zaphi/Grilloino2000/Blink_App/blynk.jpg

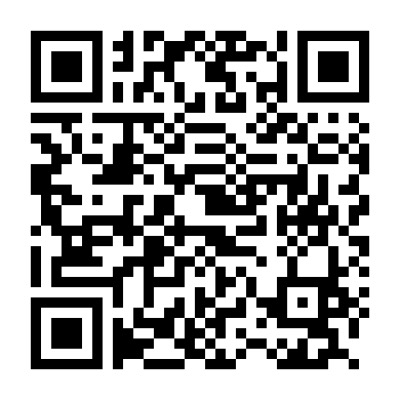
Blink_App/blynk.jpg
