zaphi/Grilloino2000/img/IMG_0674.jpg

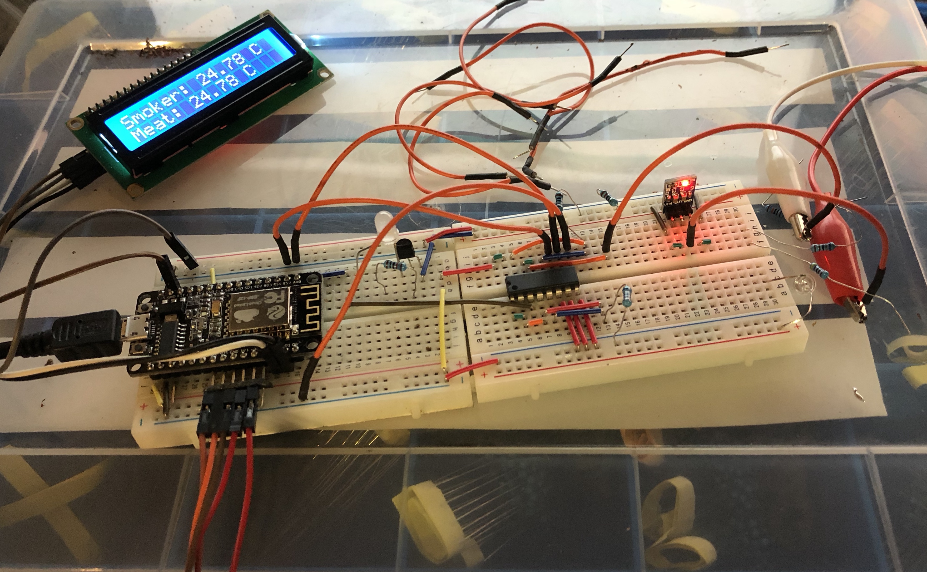
img/IMG_0674.jpg
