zaphi/Grilloino2000/img/IMG_0751.jpg

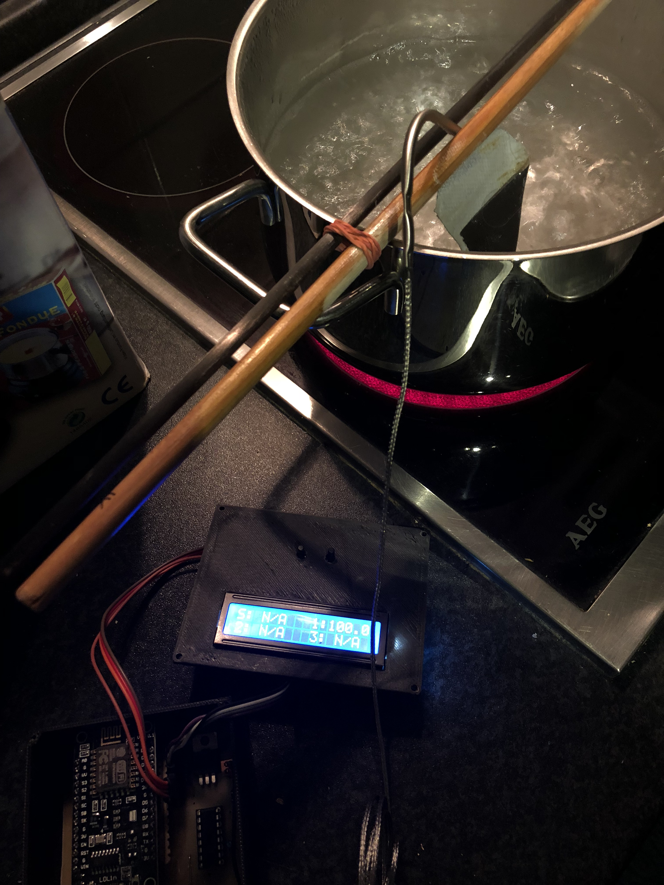
img/IMG_0751.jpg
