zaphi/Grilloino2000/img/IMG_0761.PNG

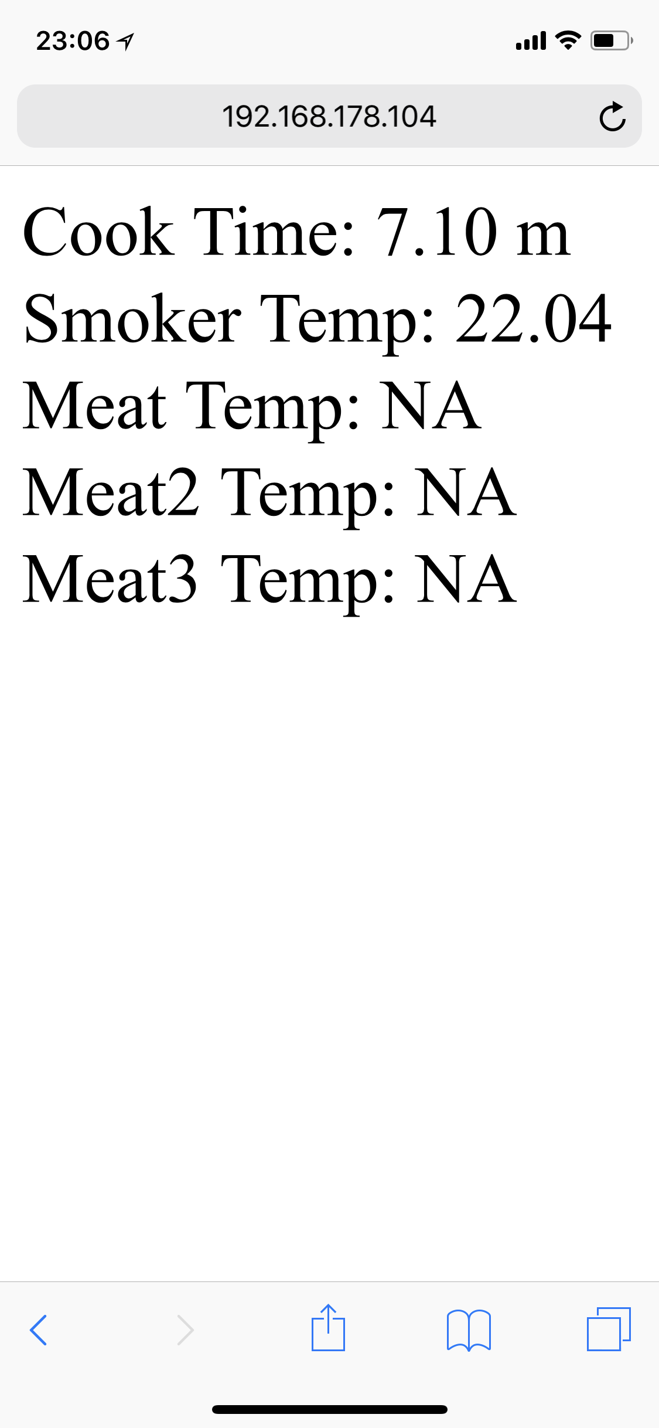
img/IMG_0761.PNG
