zaphi/Grilloino2000/img/IMG_0762.PNG

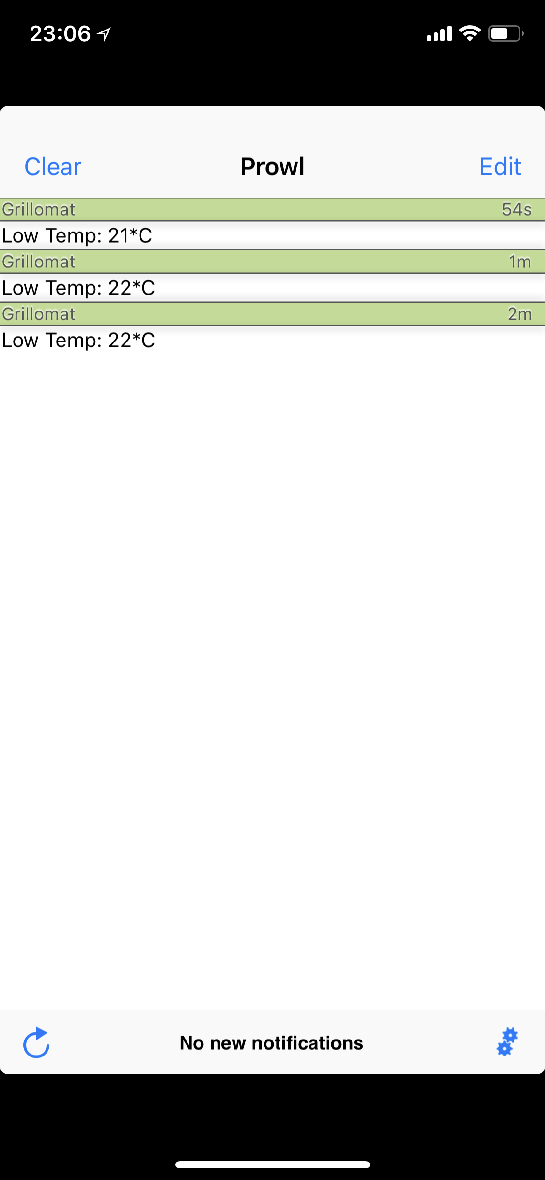
img/IMG_0762.PNG
