zaphi/Grilloino2000/img/IMG_0764.jpg

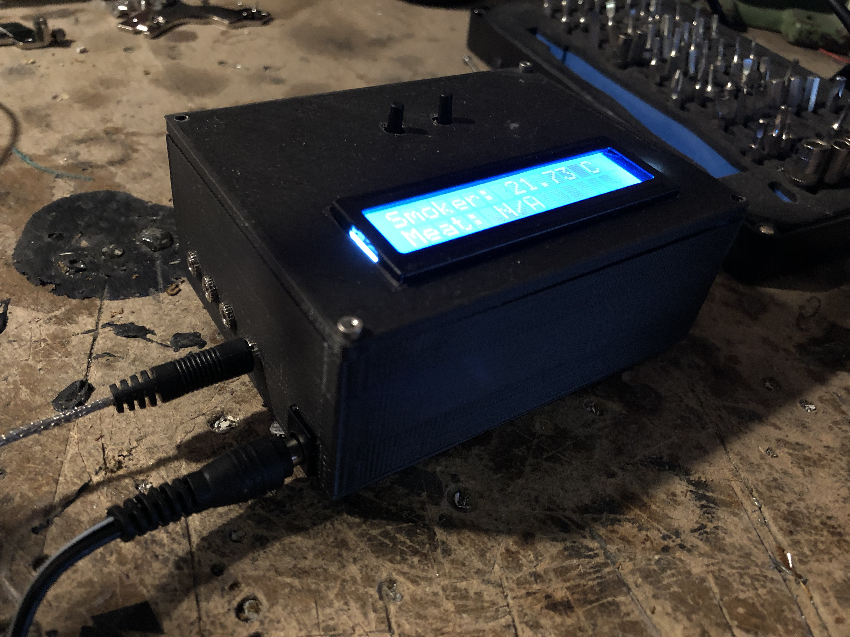
img/IMG_0764.jpg
