zaphi/Grilloino2000/img/IMG_2506.jpg

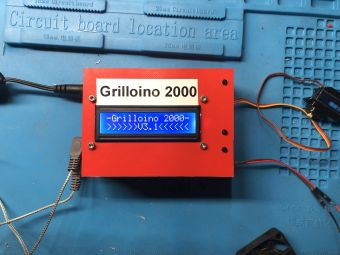
img/IMG_2506.jpg
