zaphi/Grilloino2000/img/pcb.JPG

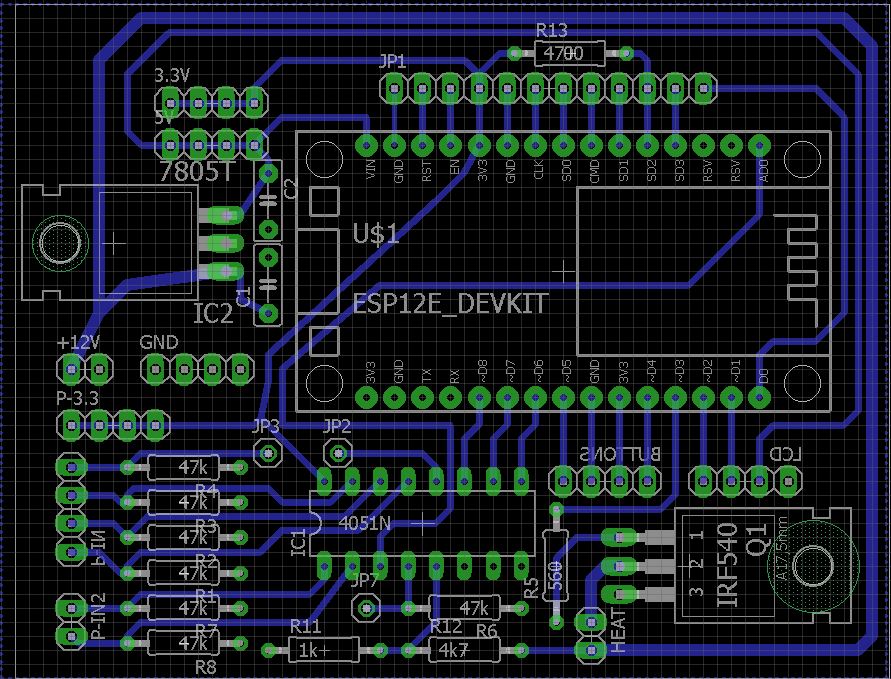
img/pcb.JPG
