zaphi/Grilloino2000/img/schaltplan.JPG

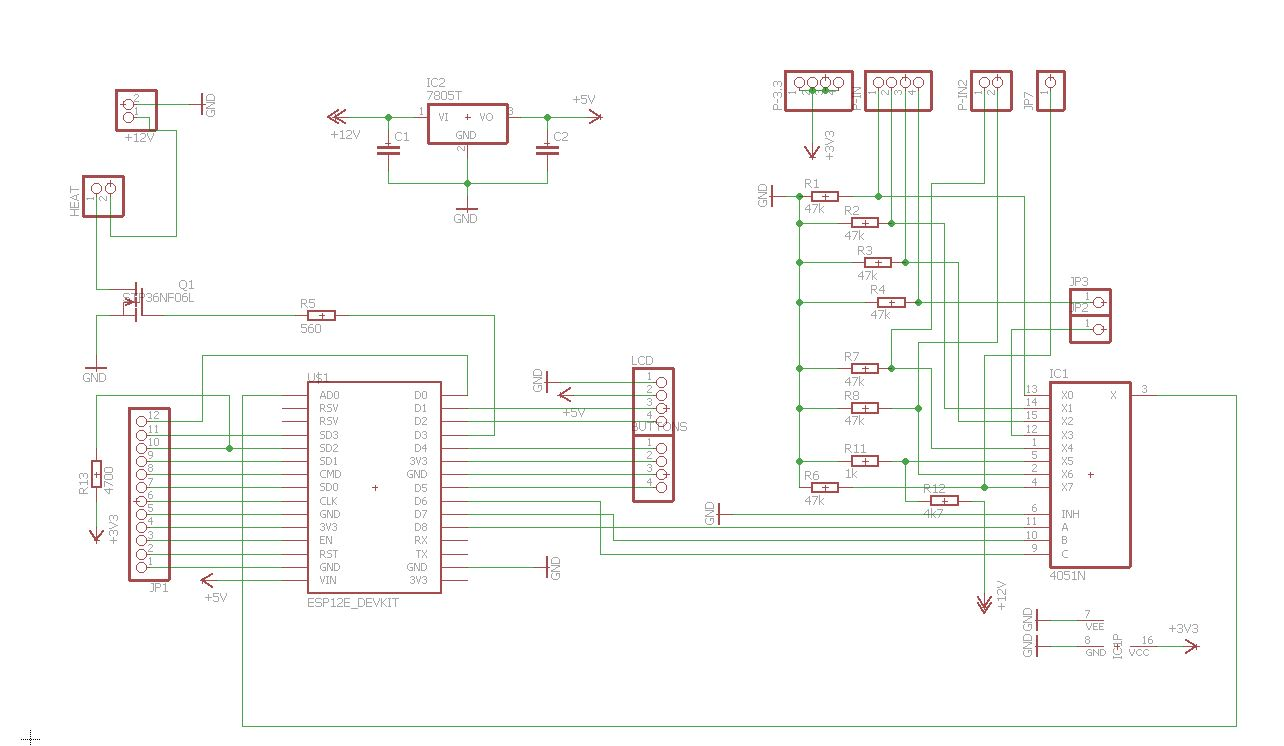
img/schaltplan.JPG
