zaphi/Grilloino2000/V3_PCB/Layout.JPG

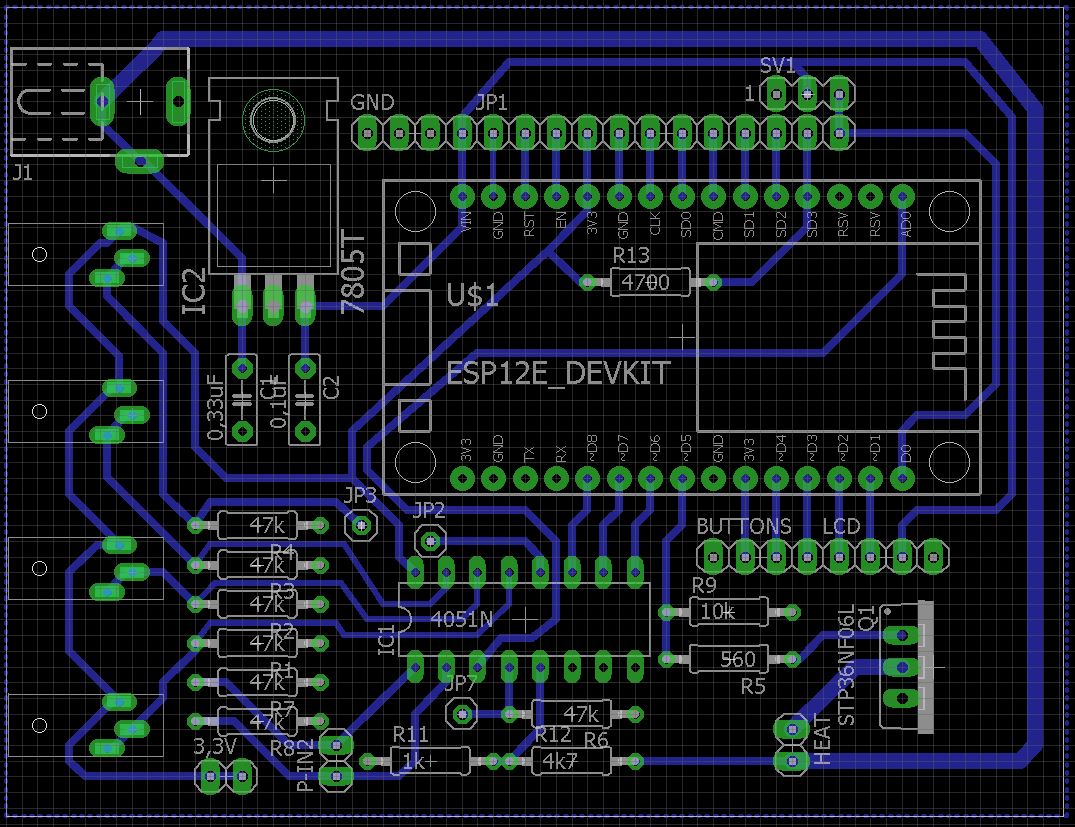
V3_PCB/Layout.JPG
