zaphi/Grilloino2000/V3_PCB/Schaltplan.JPG

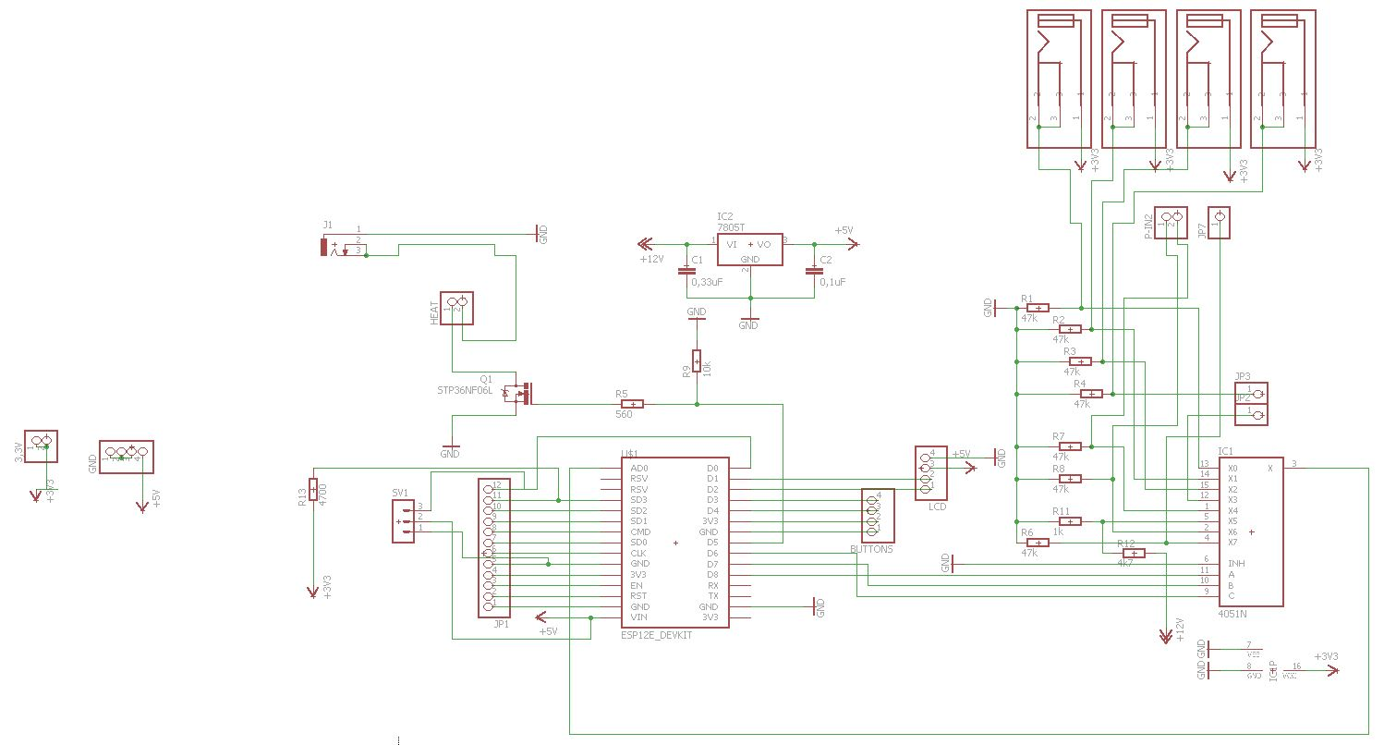
V3_PCB/Schaltplan.JPG
