zaphi/Grilloino2000/V3_Code/probe.h

#include <Arduino.h>

//Maverick ET-7/71/72/73/77/901b
float A_ET73 = 3.3566326e-03;     // "A" Coeffecient in Steinhart-Hart Equation
float B_ET73 = 2.9233209e-04;      // "B"
float C_ET73 = 4.5056748e-06;  // "C"
int rn_ET73 = 199.7;
//Maverick ET-735
float A_ET735 = 3.3566373e-03;     // "A" Coeffecient in Steinhart-Hart Equation
float B_ET735 = 1.9664428e-04;      // "B"
float C_ET735 = 9.6248678e-07;  // "C"
int rn_ET735 = 998.9;
//Maverick ET-732/733
float A_ET732 = 3.3561580e-03;     // "A" Coeffecient in Steinhart-Hart Equation
float B_ET732 = 2.2237925e-04;      // "B"
float C_ET732 = 2.6520160e-06;  // "C"
int rn_ET732 = 1004.0;
//Ikkea Fantast
float A_FANT = 3.3558340e-03;     // "A" Coeffecient in Steinhart-Hart Equation
float B_FANT = 2.5698192e-04;      // "B"
float C_FANT = 1.6391056e-06;  // "C"
int rn_FANT = 50.08;
//Ikkea Fantast neu
float A_FANTN = 3.3564021e-03;     // "A" Coeffecient in Steinhart-Hart Equation
float B_FANTN = 2.4406605e-04;      // "B"
float C_FANTN = 2.6173119e-06;  // "C"
int rn_FANTN = 230.35;
//Inkbird
float A_INKB = 3.3552456e-03;     // "A" Coeffecient in Steinhart-Hart Equation
float B_INKB = 2.5608666e-04;      // "B"
float C_INKB = 1.9317204e-06;  // "C"
int rn_INKB = 48.59;
