zaphi/Grilloino2000/img/IMG_0757.jpg

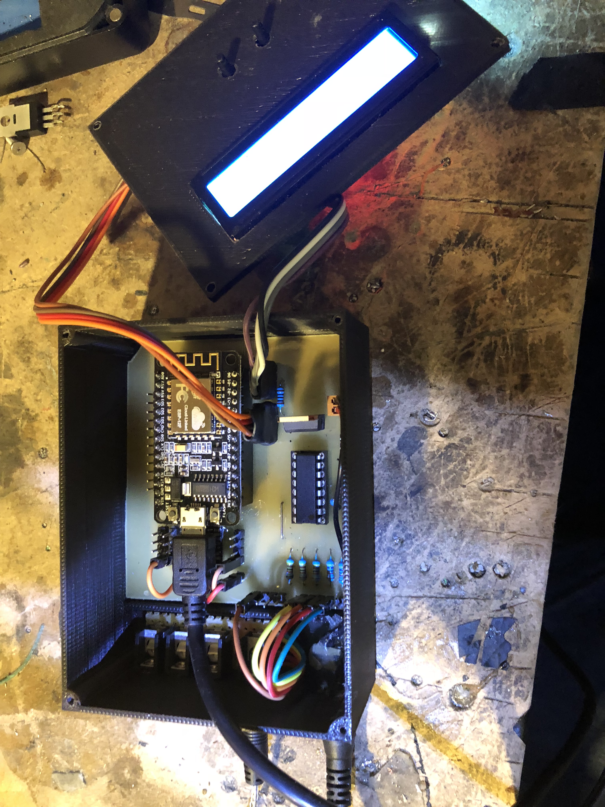
img/IMG_0757.jpg
